settinger/oh-no-doorbell/circuit/oh-no-doorbell.sch

## KiCad design circuit/oh-no-doorbell.sch (2022-03-27)

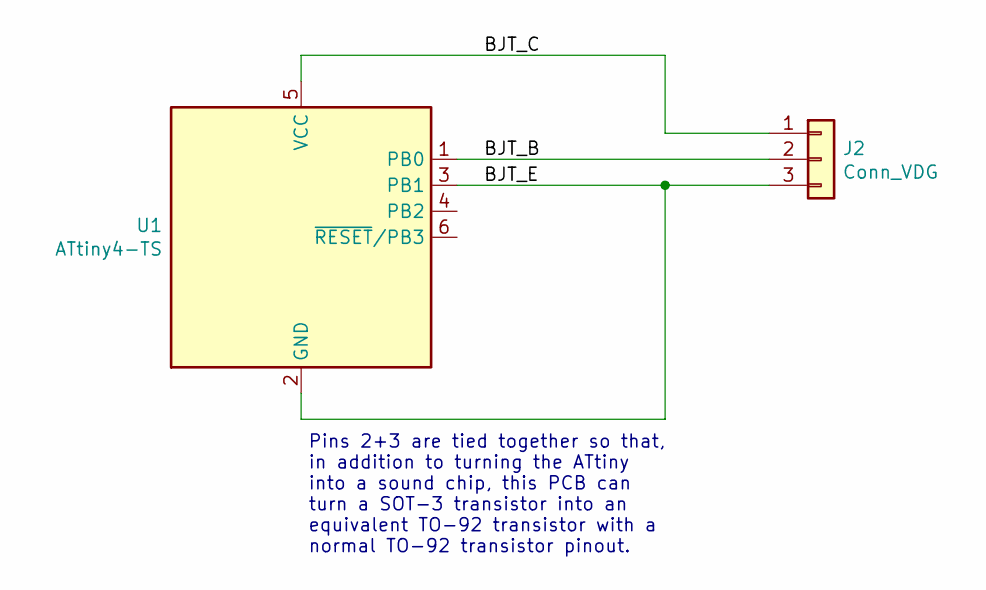
[picture p4: schematic oh-no-doorbell.sch]

Parts:
J2: Conn_VDG; TO-92_Inline
U1: ATtiny4-TS; SOT-23-6

Connections:
BJT_B: J2.2, U1.1 (PB0)
BJT_C: J2.1, U1.5 (VCC)
BJT_E: J2.3, U1.2 (GND), U1.3 (PB1)

Notes on the sheet:
Pins 2+3 are tied together so that, in addition to turning the ATtiny into a sound chip, this PCB can turn a SOT-3 transistor into an equivalent TO-92 transistor with a normal TO-92 transistor pinout.
