settinger/oh-no-doorbell/code/honk.h

/*
 * honk.h
 *
 * Created: 3/20/2022 10:03:47 PM
 *  Author: Sam
 */ 

#ifndef HONK_H_
#define HONK_H_

#include <avr/io.h>
#include <avr/pgmspace.h>

const uint8_t honk[] PROGMEM = { 0x77, 0x77, 0x77, 0x77, 0x77, 0x76, 0x66, 0x67, 0x78, 0x88, 0x87, 0x76, 0x54, 0x47, 0xaa, 0x98, 0x88, 0x86, 0x66, 0x77, 0x66, 0x78, 0x88, 0x76, 0x66, 0x77, 0x77, 0x88, 0x88, 0x77, 0x66, 0x55, 0x67, 0x77, 0x77, 0x67, 0x78, 0x77, 0x77, 0x77, 0x66, 0x77, 0x42, 0x7a, 0xc9, 0x87, 0x87, 0x76, 0x76, 0x55, 0x68, 0x98, 0x87, 0x76, 0x56, 0x78, 0x87, 0x88, 0x88, 0x76, 0x55, 0x56, 0x67, 0x78, 0x77, 0x77, 0x66, 0x77, 0x74, 0x57, 0x79, 0x78, 0x44, 0x69, 0xa9, 0x78, 0x87, 0x52, 0x37, 0xab, 0x96, 0x98, 0xa8, 0x66, 0x76, 0x56, 0x89, 0x99, 0x75, 0x54, 0x77, 0x66, 0x68, 0x88, 0x87, 0x64, 0x20, 0x59, 0xcb, 0x89, 0x78, 0x54, 0x22, 0x69, 0xbb, 0x9b, 0xaa, 0x53, 0x36, 0x77, 0x68, 0x9a, 0xb9, 0x75, 0x35, 0x54, 0x67, 0x9a, 0x98, 0x64, 0x20, 0x58, 0xa9, 0x8a, 0xa8, 0x41, 0x5, 0x9a, 0xa7, 0xbb, 0xb8, 0x42, 0x15, 0x68, 0x87, 0xac, 0xb7, 0x56, 0x56, 0x45, 0x77, 0x9a, 0x98, 0x63, 0x23, 0x76, 0x98, 0x9b, 0xa8, 0x61, 0x4, 0x89, 0xc7, 0x9b, 0xb7, 0x42, 0x15, 0x79, 0xa6, 0xab, 0xc7, 0x44, 0x55, 0x65, 0x78, 0x9b, 0xb7, 0x53, 0x25, 0x76, 0xa7, 0x9b, 0x98, 0x61, 0x6, 0x99, 0xa6, 0xba, 0xa7, 0x53, 0x23, 0x86, 0xa6, 0xac, 0xb7, 0x56, 0x65, 0x65, 0x67, 0x8a, 0xa8, 0x53, 0x6, 0x77, 0x98, 0x9a, 0x98, 0x60, 0x6, 0xa8, 0xb5, 0xcb, 0xb7, 0x43, 0x25, 0x85, 0x96, 0xbc, 0xc6, 0x55, 0x54, 0x65, 0x68, 0x9a, 0xa8, 0x54, 0x5, 0x77, 0x97, 0xab, 0xa7, 0x51, 0x7, 0x98, 0xc6, 0xcb, 0xb7, 0x31, 0x27, 0x77, 0x87, 0xbc, 0xc6, 0x55, 0x54, 0x64, 0x68, 0x9b, 0xa7, 0x54, 0x6, 0x86, 0x97, 0xbb, 0x98, 0x40,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

#define HONK_LENGTH sizeof(honk) / sizeof(honk[0])

#endif /* HONK_H_ */
